tcolar/longhorn/pics/micro_pro.jpg

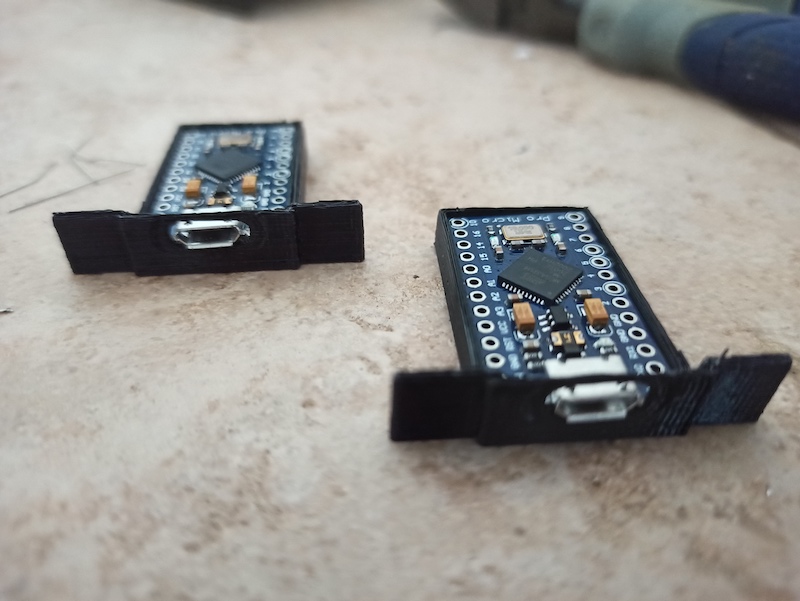
pics/micro_pro.jpg
