tcolar/longhorn/pics/wired.jpg

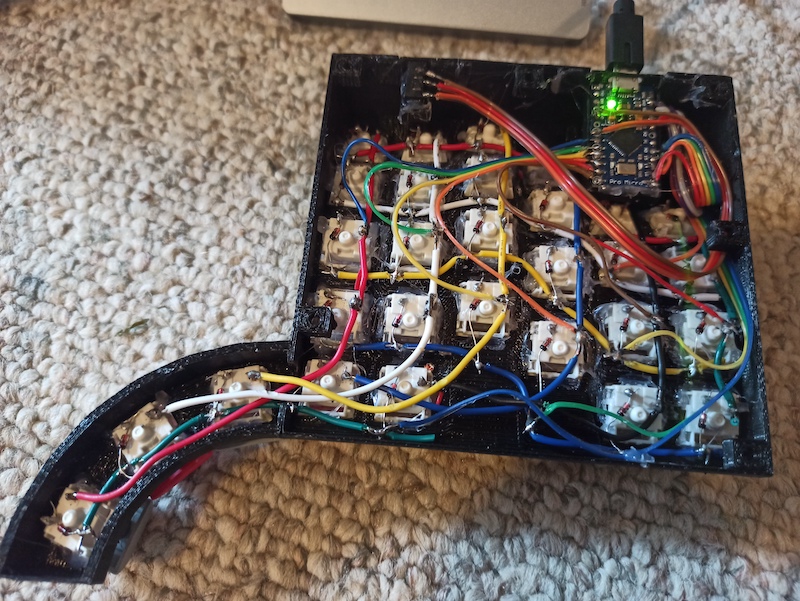
pics/wired.jpg
